ml8/3x3/hardware/img/socket-pad-solder1.jpeg

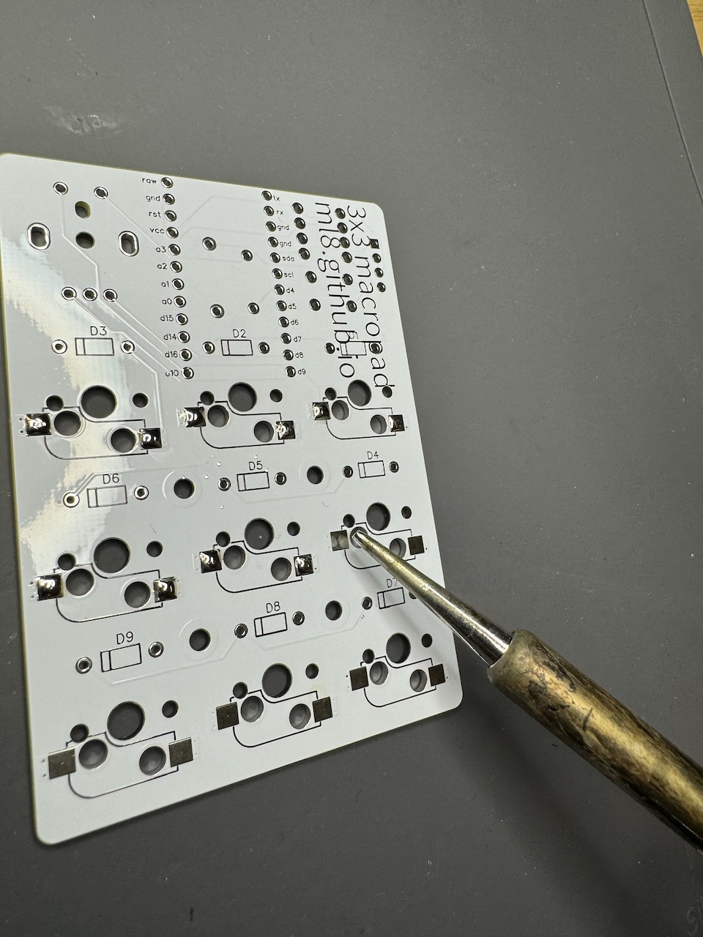
hardware/img/socket-pad-solder1.jpeg
